team-somehow/eth-arcade/design/box-run-live/aiming.png

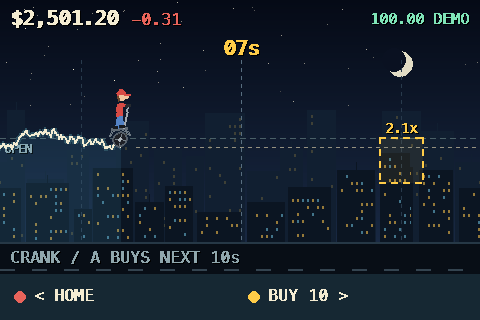
design/box-run-live/aiming.png
