team-somehow/eth-arcade/design/box-run-live/bought.png

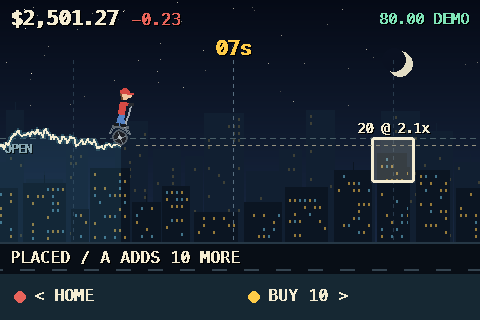
design/box-run-live/bought.png
