team-somehow/eth-arcade/design/box-run-live/hattrick.gif

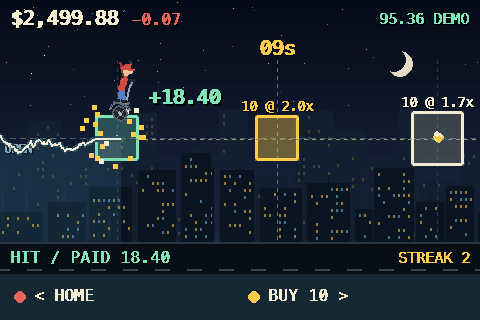
design/box-run-live/hattrick.gif
