team-somehow/eth-arcade/design/box-run-live/hattrick.png

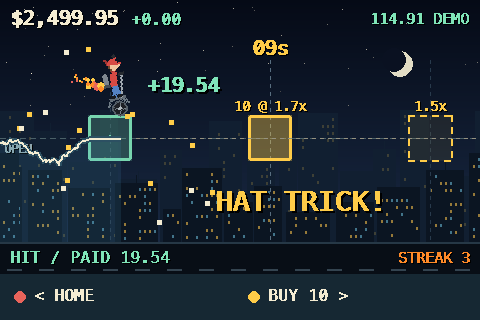
design/box-run-live/hattrick.png
