team-somehow/eth-arcade/design/box-run-live/home.png

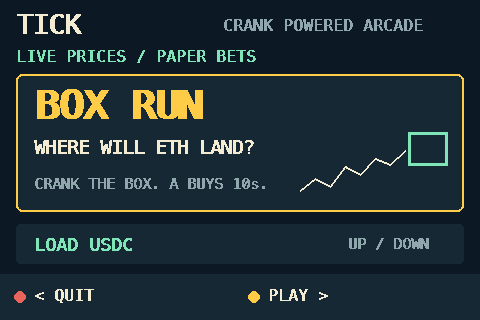
design/box-run-live/home.png
