team-somehow/eth-arcade/design/box-run-live/live.png

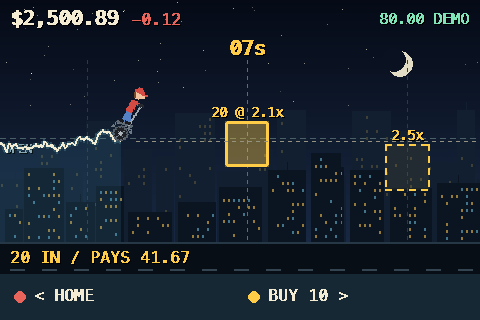
design/box-run-live/live.png
