team-somehow/eth-arcade/design/box-run-live/miss.png

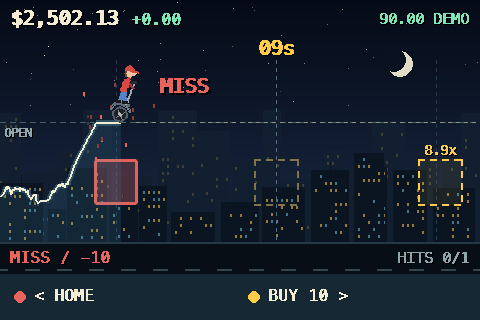
design/box-run-live/miss.png
