team-somehow/eth-arcade/design/box-run-live/waiting.png

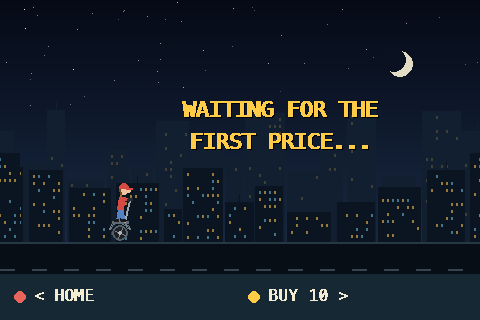
design/box-run-live/waiting.png
