team-somehow/eth-arcade/design/box-run-live/wallet.png

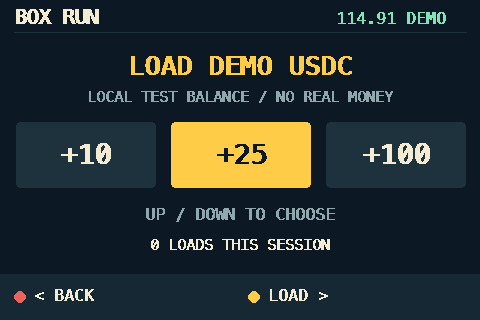
design/box-run-live/wallet.png
