team-somehow/eth-arcade/design/box-run-storyboard/outcomes.png

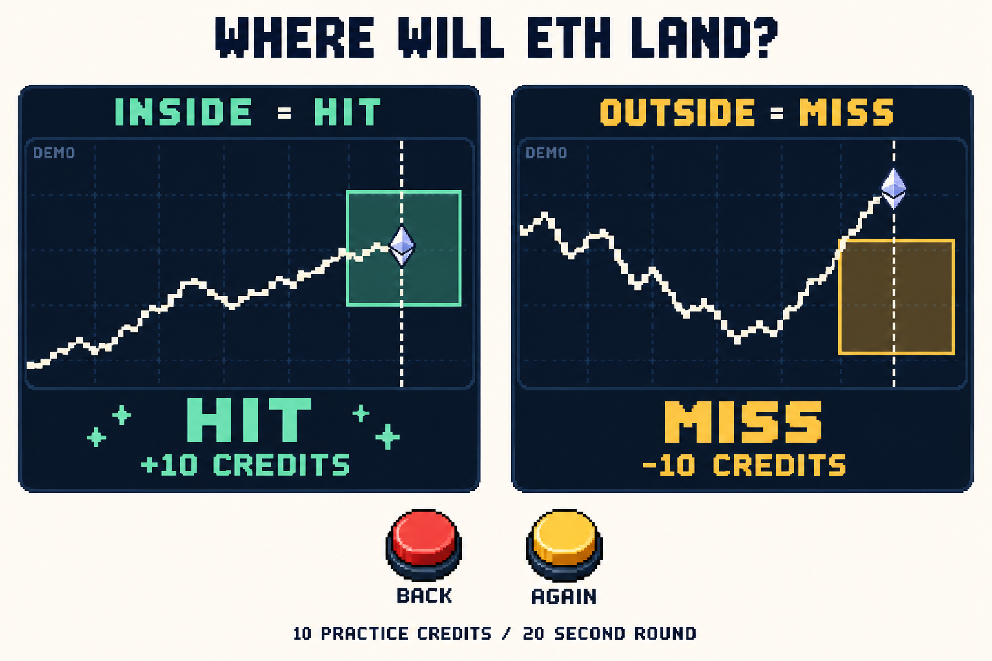
design/box-run-storyboard/outcomes.png
