team-somehow/eth-arcade/design/box-run-storyboard/round.png

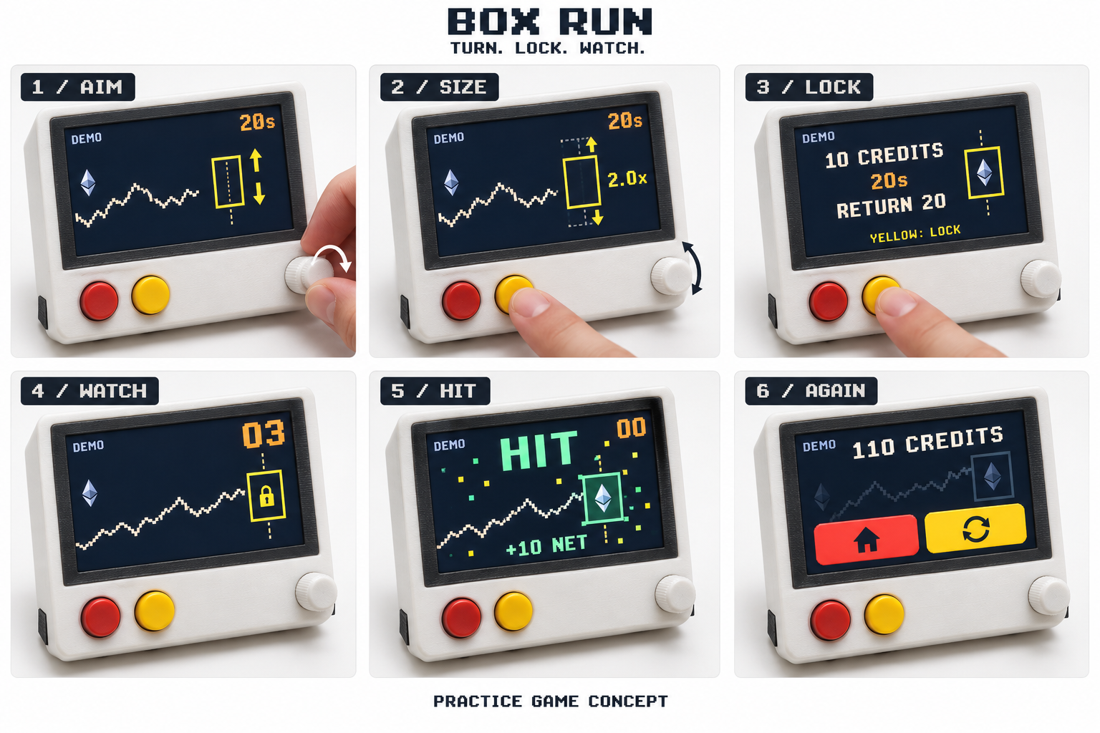
design/box-run-storyboard/round.png
