team-somehow/eth-arcade/design/brand/eth-arcade-cover-640x360.png

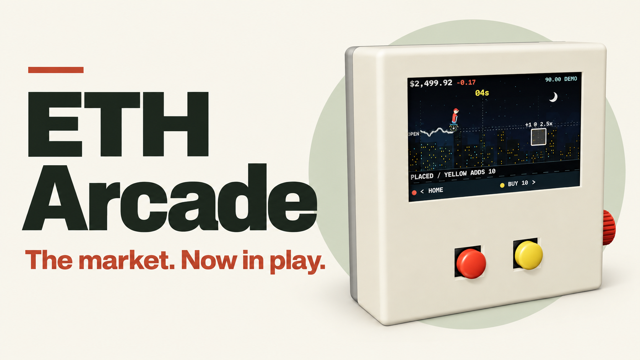
design/brand/eth-arcade-cover-640x360.png
