team-somehow/eth-arcade/design/cad/back.png

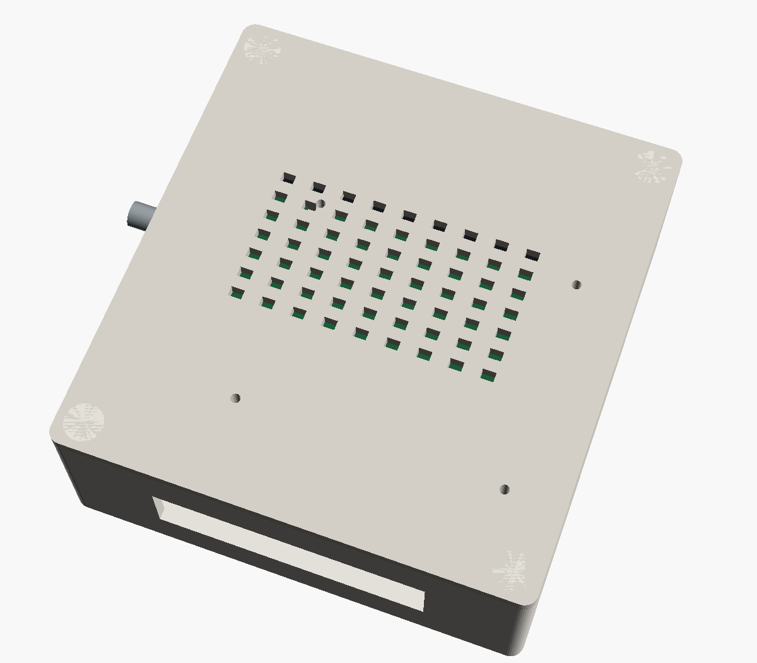
design/cad/back.png
