team-somehow/eth-arcade/design/cad/bracket.png

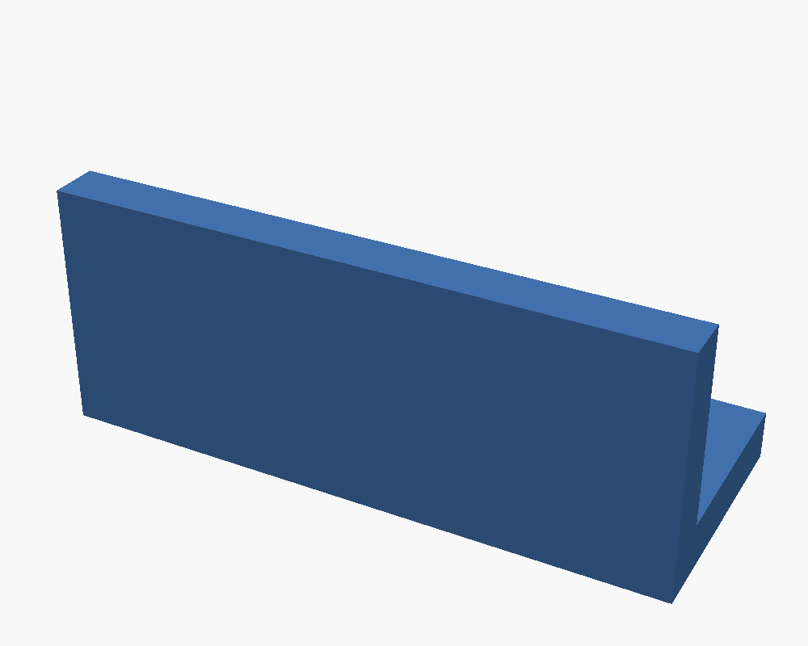
design/cad/bracket.png
