team-somehow/eth-arcade/design/cad/exploded.png

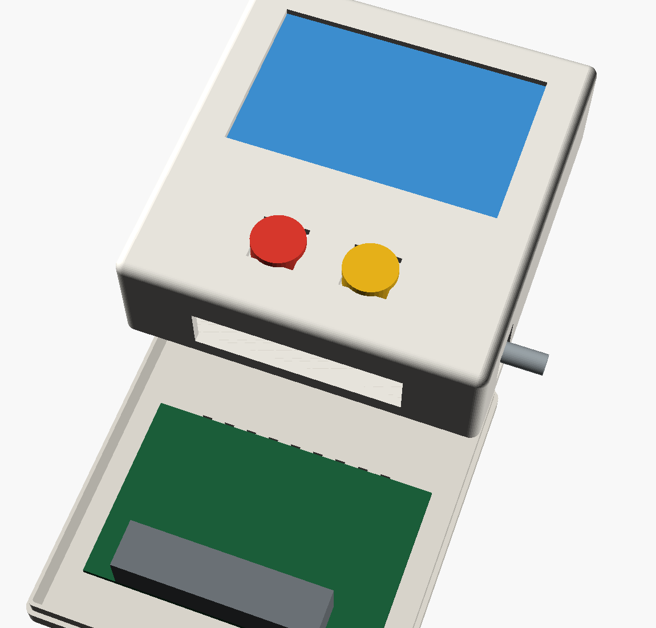
design/cad/exploded.png
