team-somehow/eth-arcade/design/cad/front.png

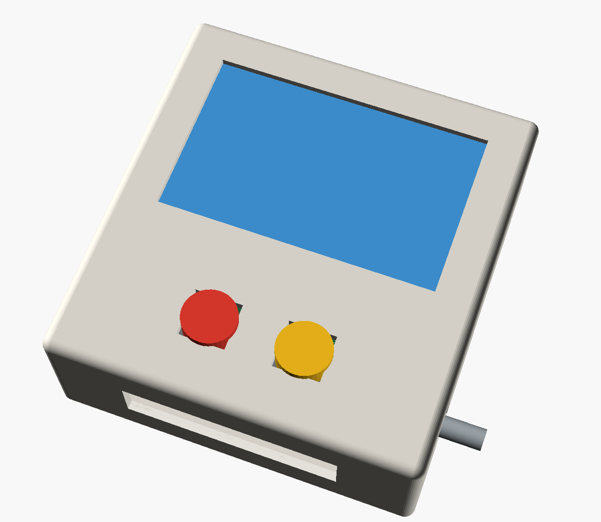
design/cad/front.png
