team-somehow/eth-arcade/design/cad/open.png

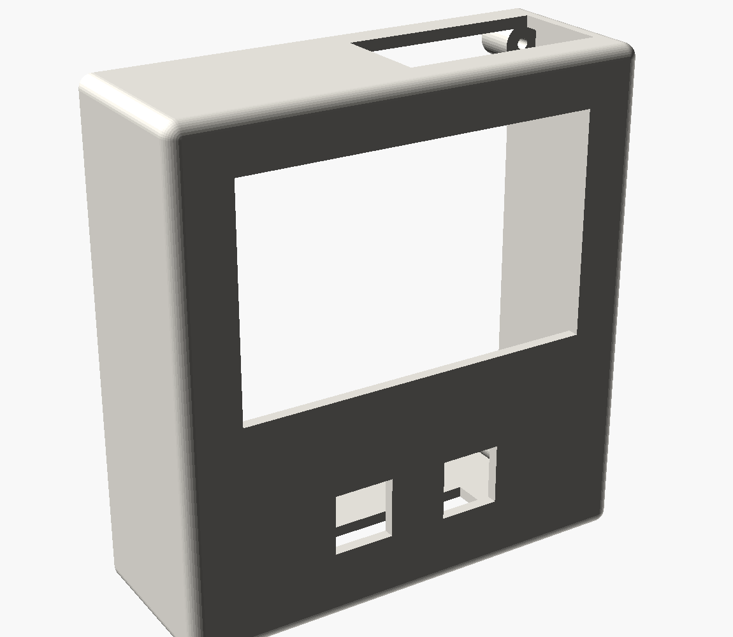
design/cad/open.png
