team-somehow/eth-arcade/design/cad/tick-case-2d.png

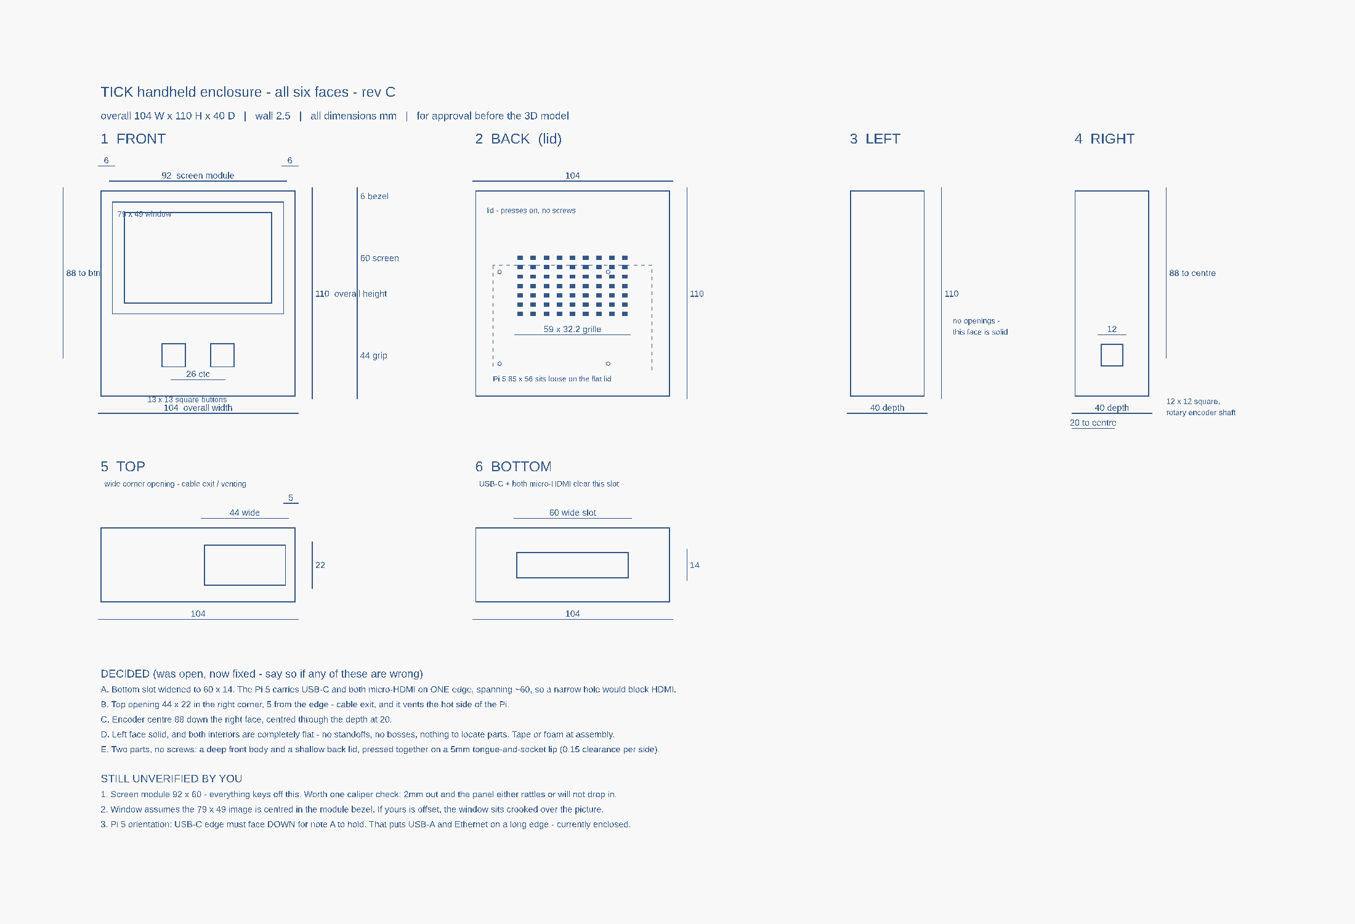
design/cad/tick-case-2d.png
