team-somehow/eth-arcade/design/render-round-2/01-cream-cartridge.png

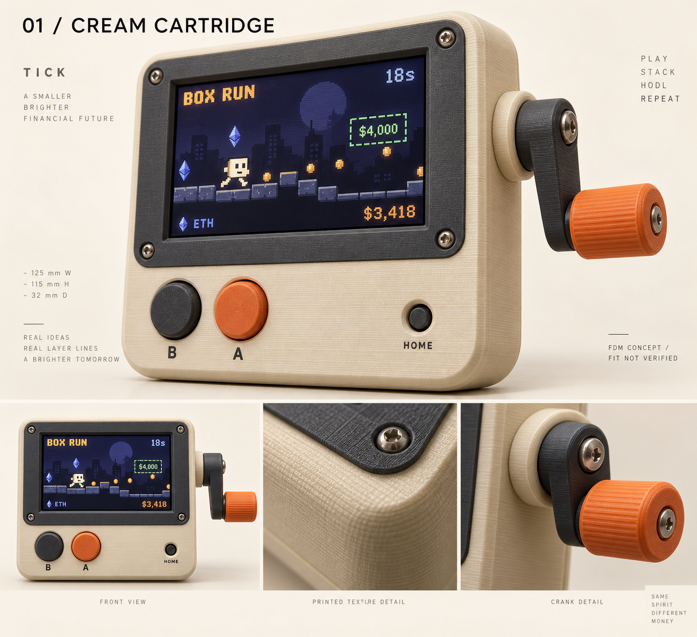
design/render-round-2/01-cream-cartridge.png
