team-somehow/eth-arcade/design/render-round-2/02-graphite-terminal.png

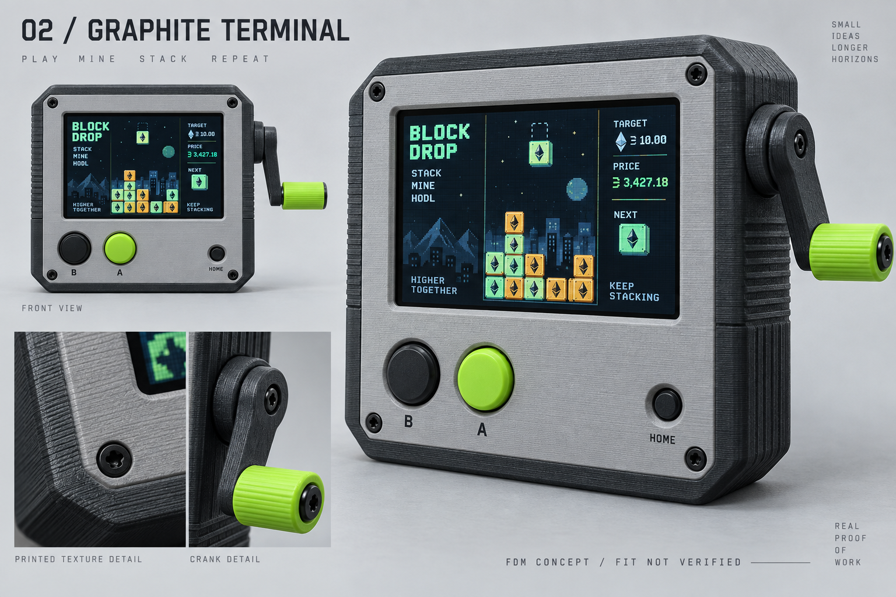
design/render-round-2/02-graphite-terminal.png
