team-somehow/eth-arcade/design/render-round-2/04-game-concepts.png

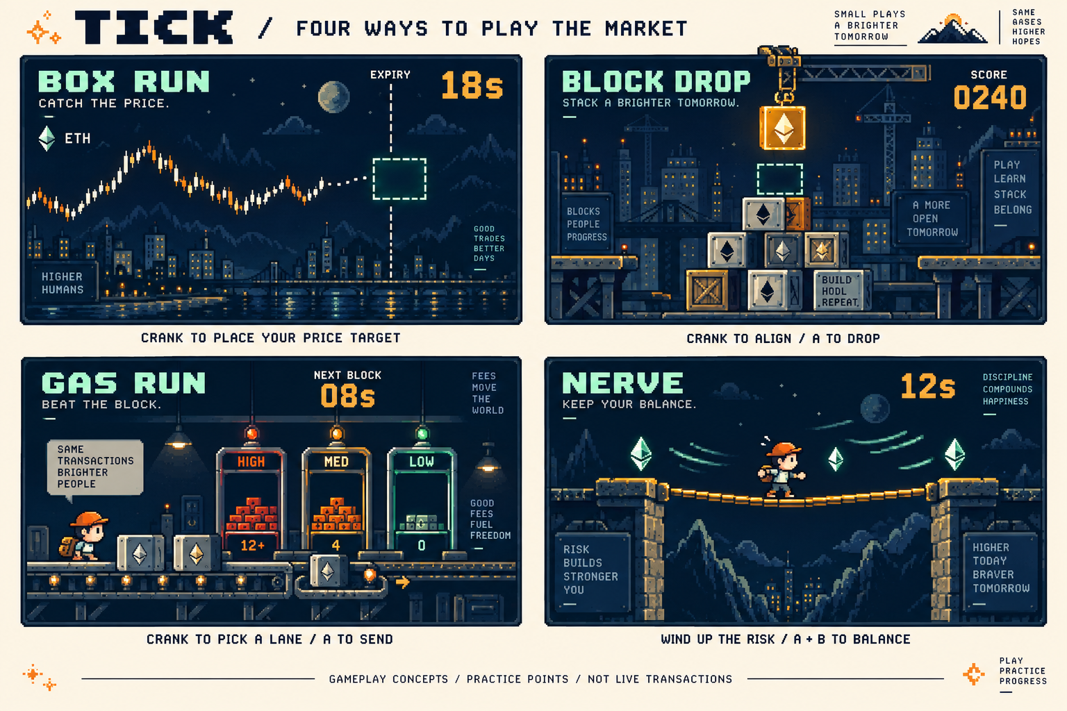
design/render-round-2/04-game-concepts.png
