team-somehow/eth-arcade/design/screen-studies.png

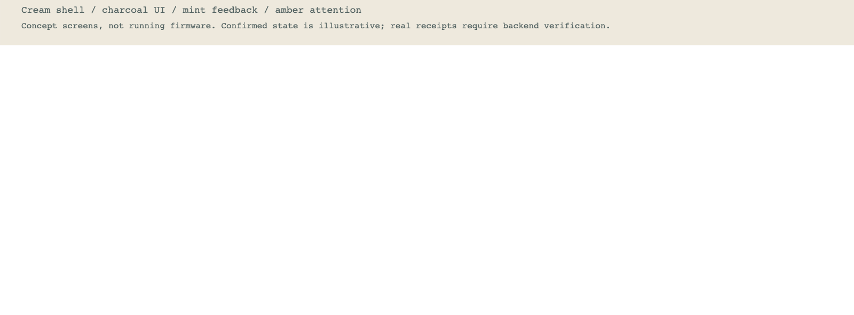
design/screen-studies.png
