team-somehow/eth-arcade/design/tick-device-concept.png

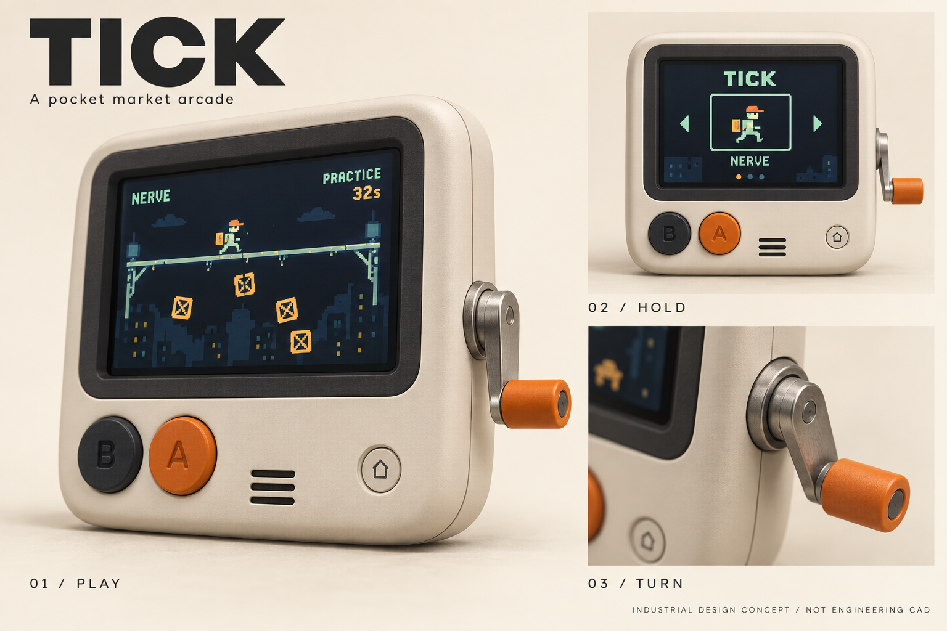
design/tick-device-concept.png
