team-somehow/eth-arcade/design/box-run-build/aim.png

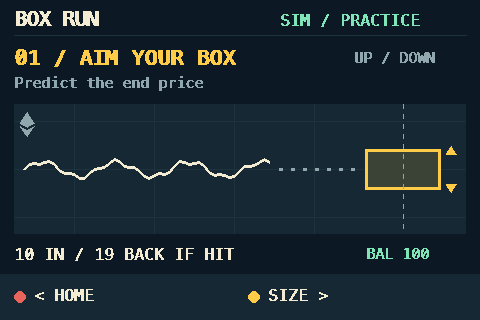
design/box-run-build/aim.png
