team-somehow/eth-arcade/design/box-run-build/empty.png

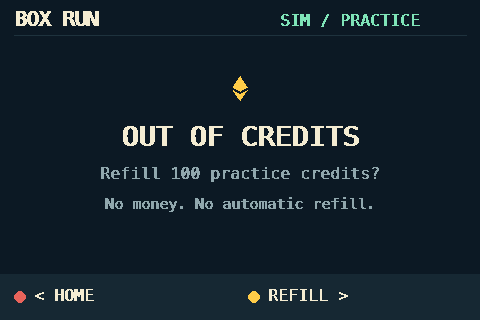
design/box-run-build/empty.png
