team-somehow/eth-arcade/design/box-run-build/gameplay-sheet.png

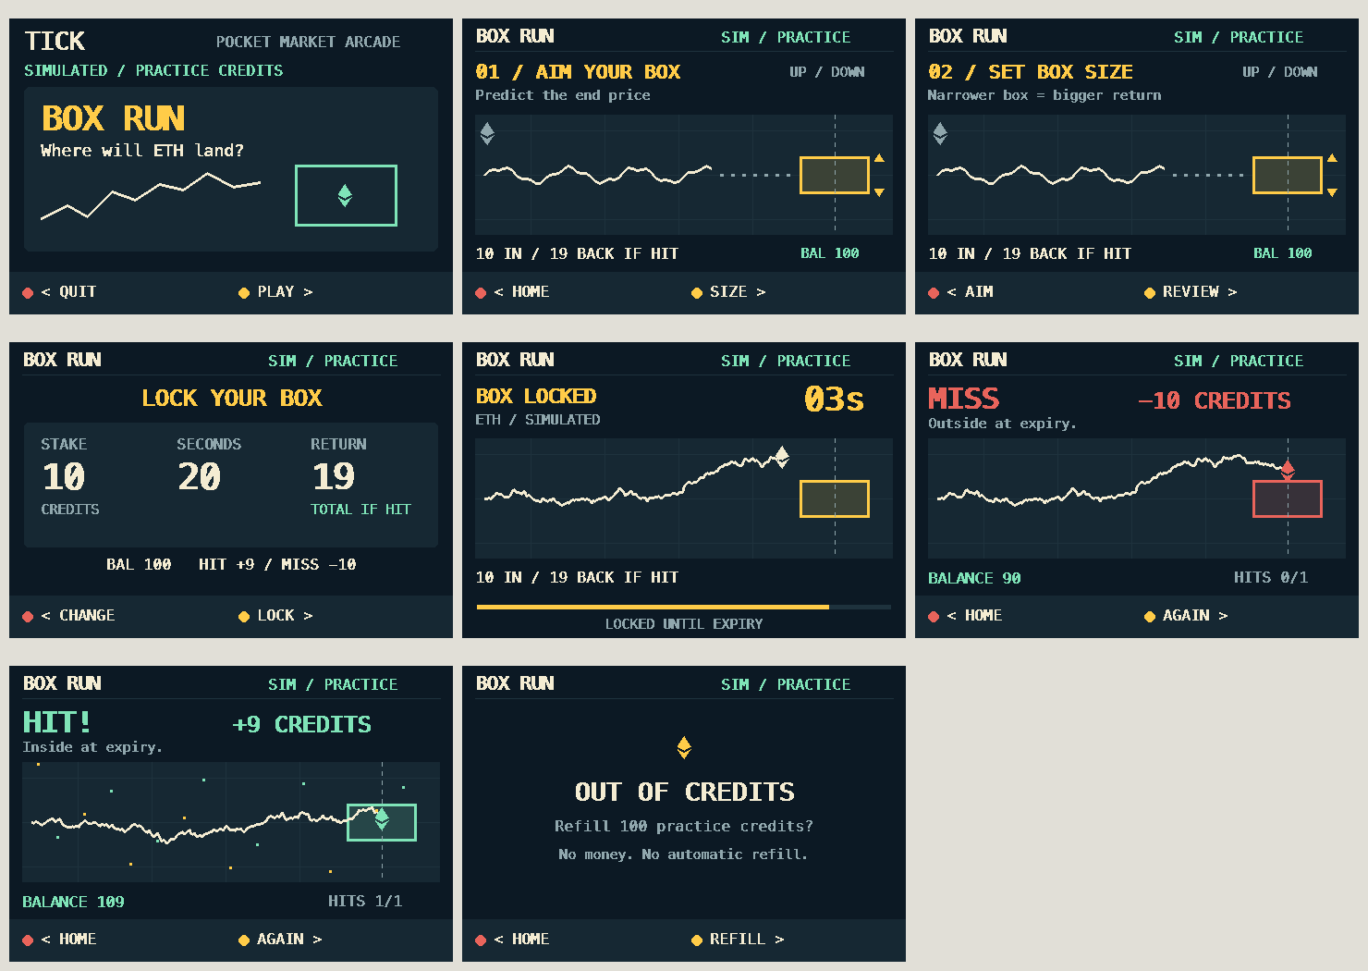
design/box-run-build/gameplay-sheet.png
