team-somehow/eth-arcade/design/box-run-build/hit.png

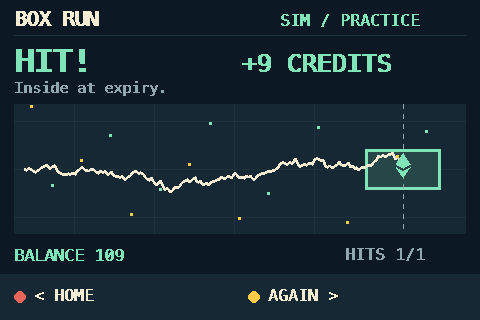
design/box-run-build/hit.png
