team-somehow/eth-arcade/design/box-run-build/home.png

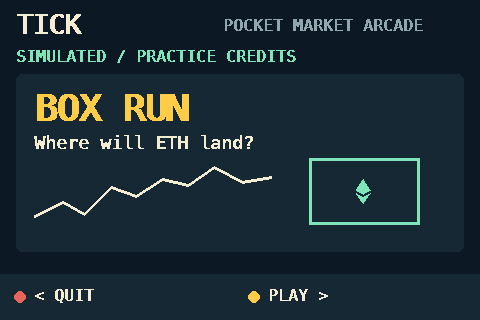
design/box-run-build/home.png
