team-somehow/eth-arcade/design/box-run-build/miss.png

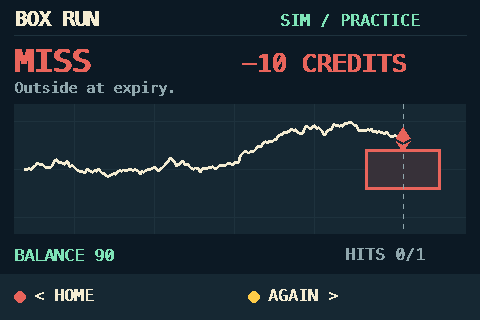
design/box-run-build/miss.png
