team-somehow/eth-arcade/design/box-run-build/review.png

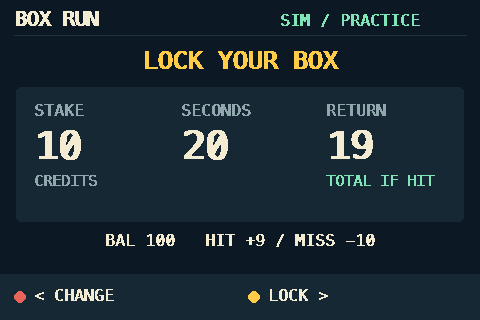
design/box-run-build/review.png
