team-somehow/eth-arcade/design/box-run-build/running.png

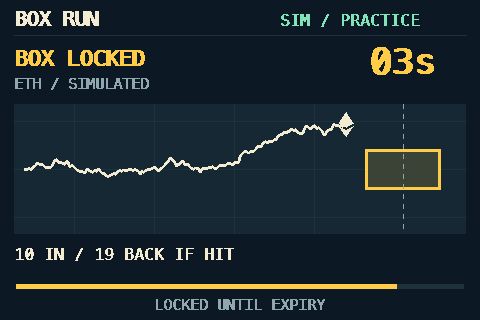
design/box-run-build/running.png
