team-somehow/eth-arcade/design/cad/print-layout.png

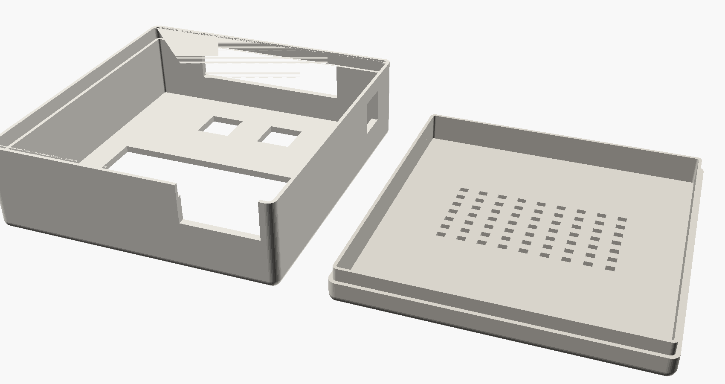
design/cad/print-layout.png
