team-somehow/eth-arcade/design/practical-crank/assembly.png

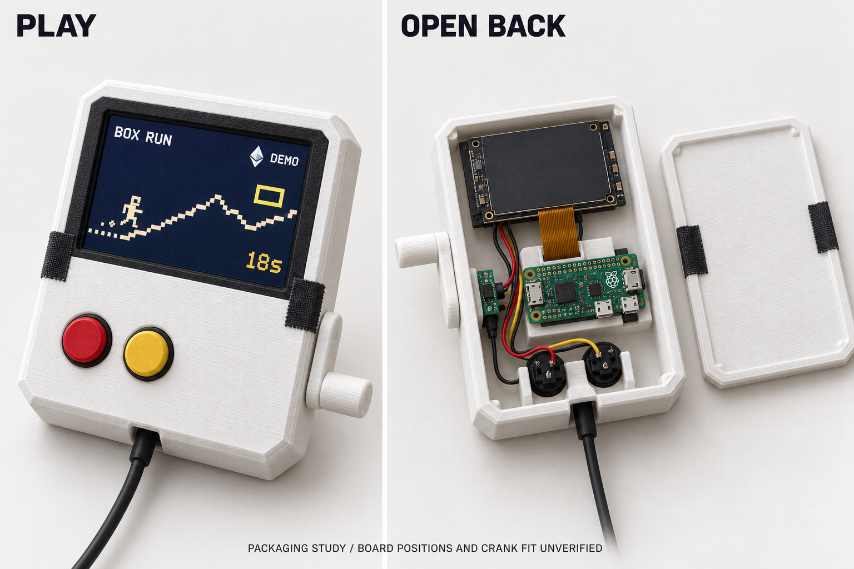
design/practical-crank/assembly.png
