team-somehow/eth-arcade/design/rush-build/arming.png

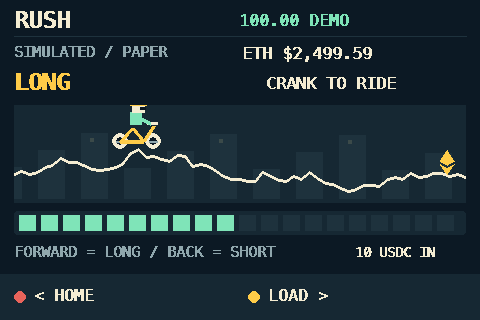
design/rush-build/arming.png
