team-somehow/eth-arcade/design/rush-build/gameplay-sheet.png

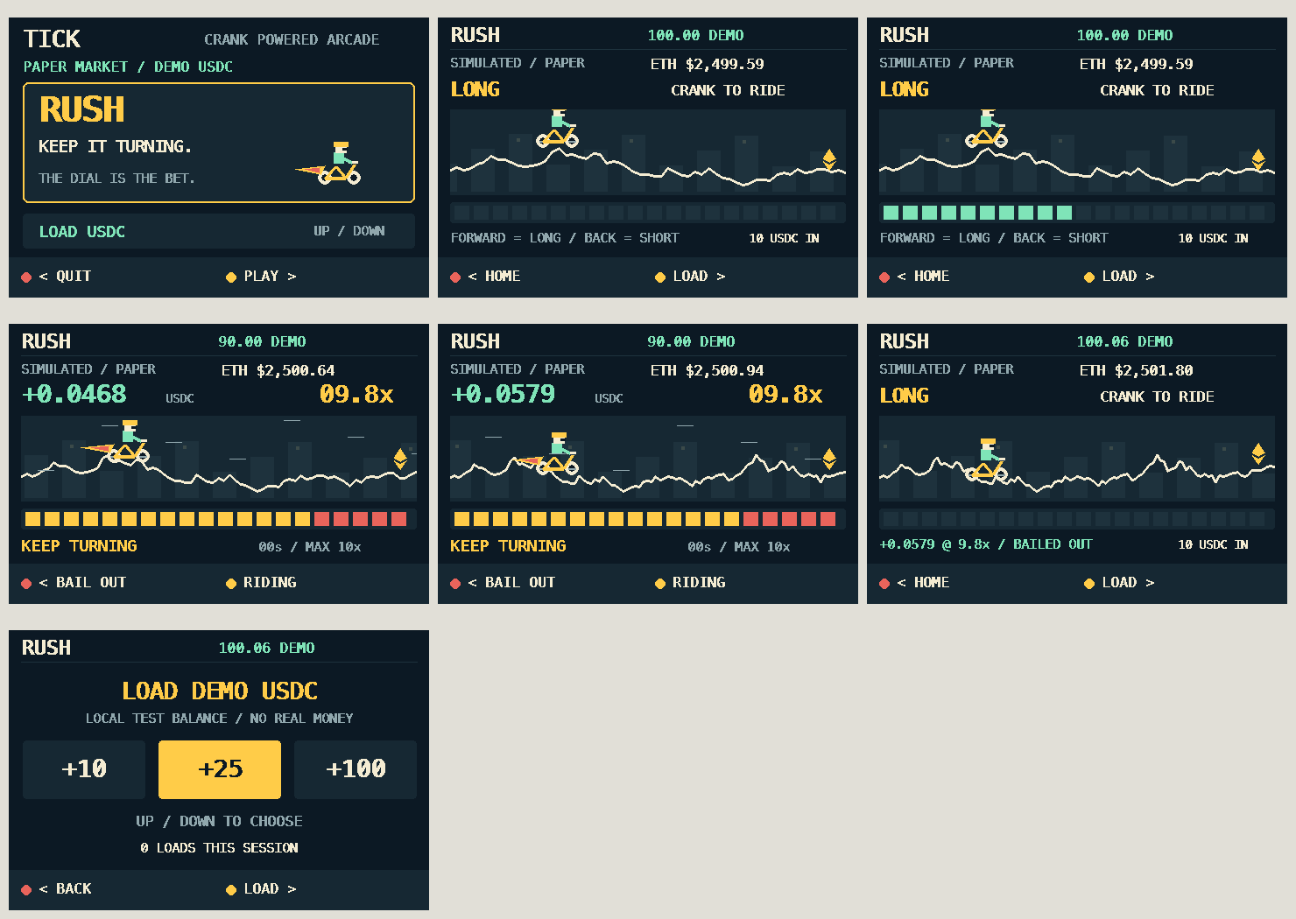
design/rush-build/gameplay-sheet.png
