team-somehow/eth-arcade/design/rush-build/redline.png

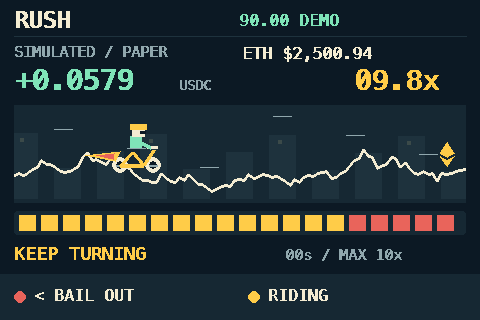
design/rush-build/redline.png
