team-somehow/eth-arcade/design/rush-build/riding.png

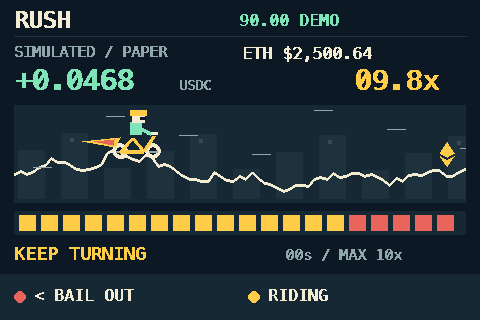
design/rush-build/riding.png
