team-somehow/eth-arcade/design/rush-build/settled.png

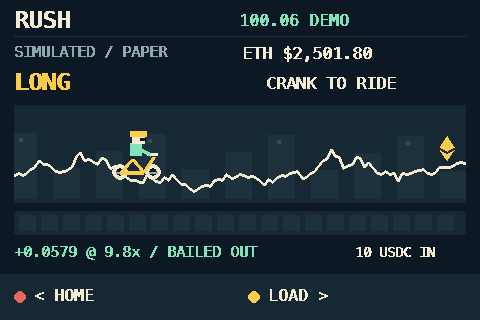
design/rush-build/settled.png
