team-somehow/eth-arcade/design/rush-build/wallet.png

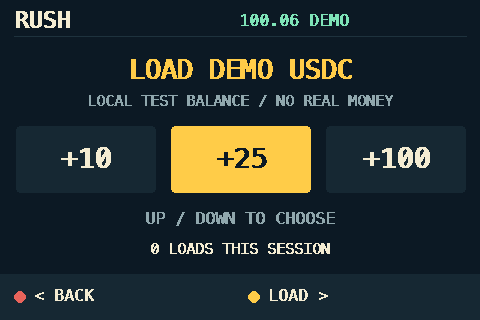
design/rush-build/wallet.png
