team-somehow/eth-arcade/design/tick-tape-build.png

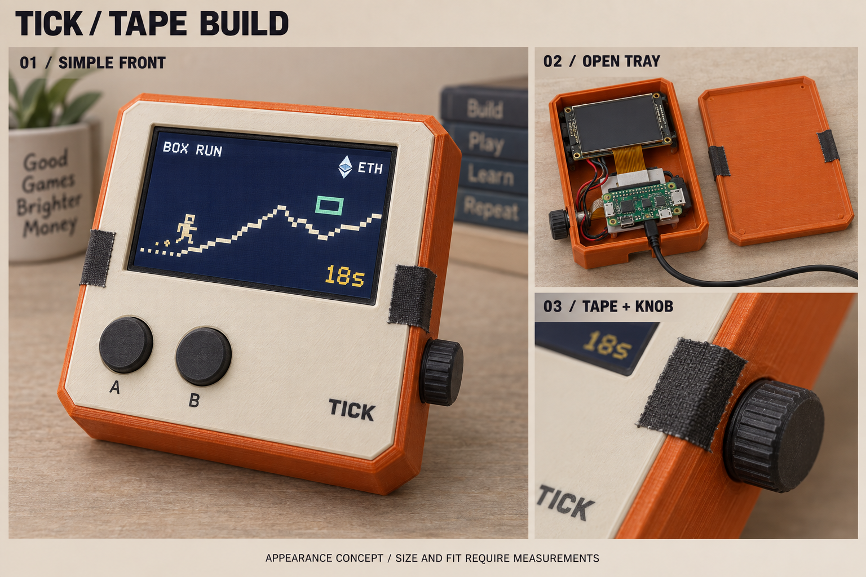
design/tick-tape-build.png
